ImogenWren/i2c-arduino-daq/i2c-arduino-dac-firmware/STC31.h

/* # Sensirion SEK-STC31 - CO2 Sensor - i2c

- 5v or 3.3v (calibrated for 3.3v)

 - Pinout:
 
	- Vdd:    green
	- SCL:    brown
	- GND: 	  pink
	- SDA:   Yellow
 */


#ifndef STC31_h
#define STC31_h



#include <SensirionI2CStc3x.h>


class STC31 {
public:

  SensirionI2CStc3x stc3x;


  struct stc31_Data {
    float gasConcentration;
    float gasTemperature;
  };

  //Constructor
  STC31() {
    // SHTSensor sht4x(SHTSensor::SHT4X);
  }

  STC31(const char _sensorID[8]) {
    strcpy(ID, _sensorID);
  }

  char ID[8] = { "STC31" };



  void stc31_Setup();

  stc31_Data stc31_Loop();  // This does return data but now its inside class can just access object globals directly




private:
};














#endif
