ImogenWren/i2c-arduino-daq/i2c-arduino-dac-firmware/i2c-utils.h

#include <SparkFun_I2C_Mux_Arduino_Library.h>  //Click here to get the library: http://librarymanager/All#SparkFun_I2C_Mux

QWIICMUX sensorMux;  // Create instance of i2c mux


void setupMux() {
  Wire.begin();
  if (sensorMux.begin(0x70, Wire) == false) {
    Serial.println(F("Mux not detected"));
    while (1) {
      Serial.println(F("Please Reset Arduino"));
      delay(5000);
    }
  }
  // Serial.println("Mux detected");
  delay(50);
}



byte checkMuxPort() {
  byte currentChannel = sensorMux.getPort();
  //  Serial.print("CurrentChannel: ");
  //  Serial.println(currentChannel);
  return currentChannel;
}

/*
void i2c_scanner() {
  Serial.println();

  byte nDevices = 0;
  for (byte address = 1; address < 127; address++) {
    Wire.beginTransmission(address);
    byte error = Wire.endTransmission();

    if (error == 0) {
      Serial.print(F("I2C device found at address 0x"));
      if (address < 0x10) {
        Serial.print("0");
      }
      Serial.print(address, HEX);
      Serial.println();

      nDevices++;
    } else if (error == 4) {
      Serial.print(F("Unknown error at address 0x"));
      if (address < 0x10) {
        Serial.print("0");
      }
      Serial.println(address, HEX);
    }
  }

  if (nDevices == 0) {
    Serial.println(F("No I2C devices found"));
  } else {
    Serial.println(F("Done"));
  }

  delay(100);
}

*/
